KrouzkyTIB/ParentsRobots/SW/src/Server/ServerHandler.h

//
// Created by jiri on 10.9.22.
//

#ifndef SW_COMMUNICATION_HANDLER_H
#define SW_COMMUNICATION_HANDLER_H
#define NUMBER_OF_SSIDS 8

#include "Arduino.h"
#include <WiFi.h>
#include <WebServer.h>

class ServerHandler {
private:
    std::string ssid;
    static const std::string ssidNames[NUMBER_OF_SSIDS];
    uint8_t channel;
    static const IPAddress localIp;
    static const IPAddress gateway;
    static const IPAddress subnet;
    static String bundleJs;
    static String indexHtml;
    static WebServer server;

private:
    static void handleIndexHTMLServe();
    static void handleBundleJsServe();
    static void readString(String filename, String * buffer);
    static void handleData();

public:
    void init(uint8_t ssidIndex);
    void handleClient();
};

#endif //SW_COMMUNICATION_HANDLER_H
